cj667113/LoPRTS/LoPRTS_Photos/IMG_20190118_013232048.jpg

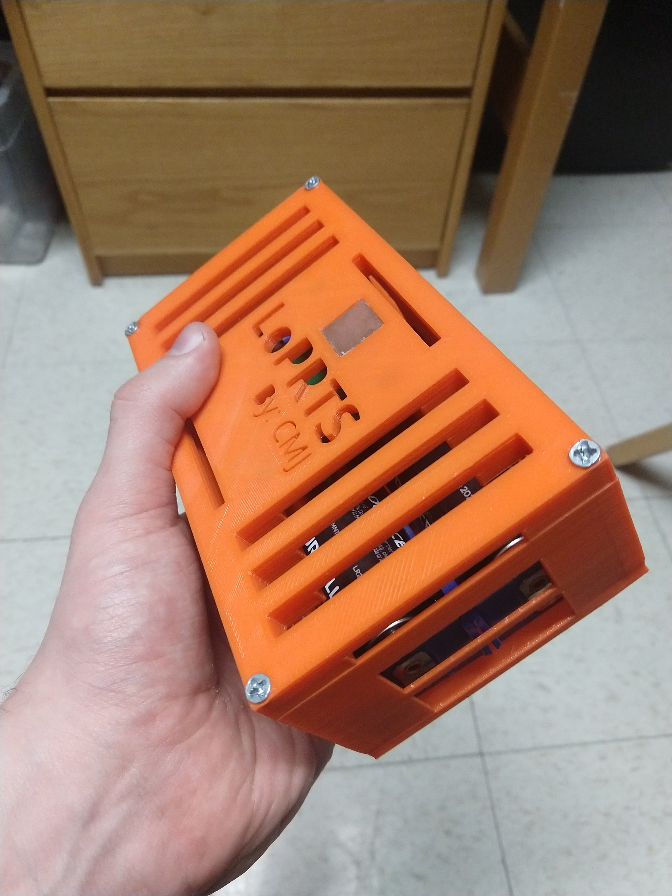
LoPRTS_Photos/IMG_20190118_013232048.jpg
