cj667113/LoPRTS/LoPRTS_Photos/IMG_20190118_013233164.jpg

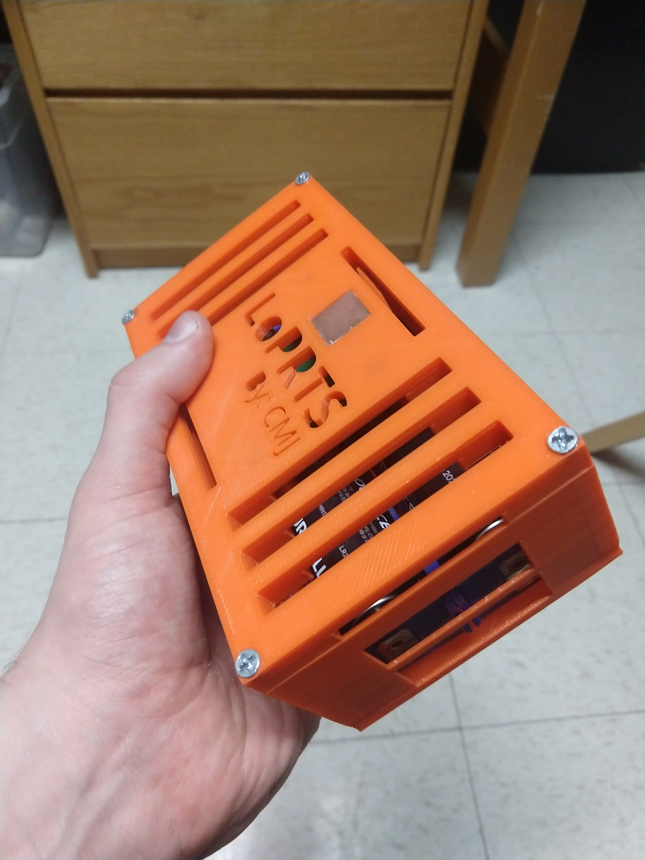
LoPRTS_Photos/IMG_20190118_013233164.jpg
