cj667113/LoPRTS/LoPRTS_Photos/IMG_20190122_004202089.jpg

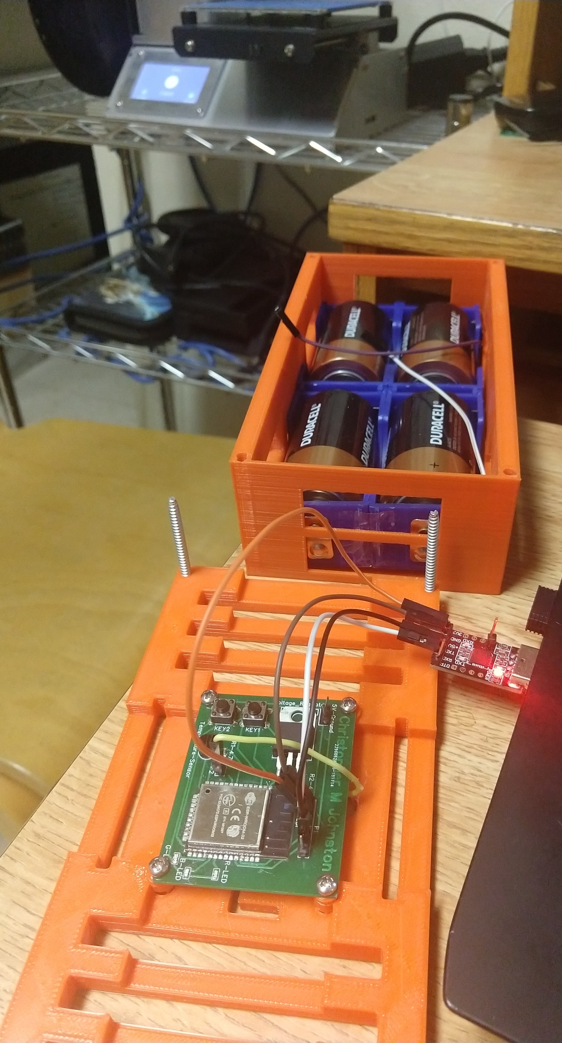
LoPRTS_Photos/IMG_20190122_004202089.jpg
