cj667113/LoPRTS/LoPRTS_Photos/IMG_20190122_004248606.jpg

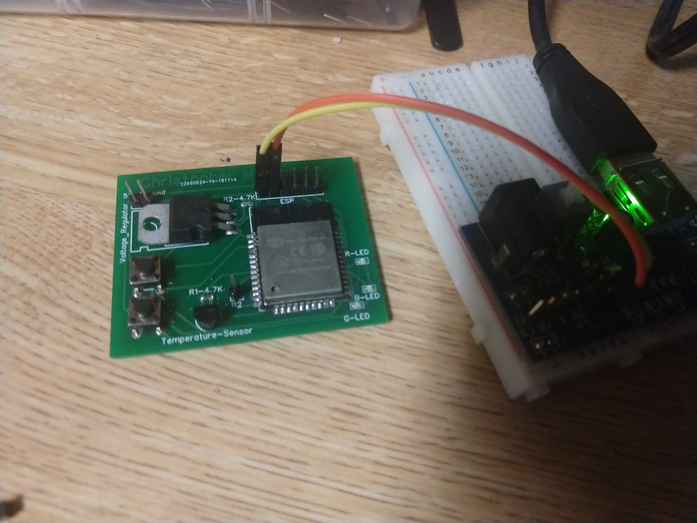
LoPRTS_Photos/IMG_20190122_004248606.jpg
